SeanP2001/Sunrise_Alarm_Clock_V3/Code/Documentation/latex/App_8h__incl.pdf

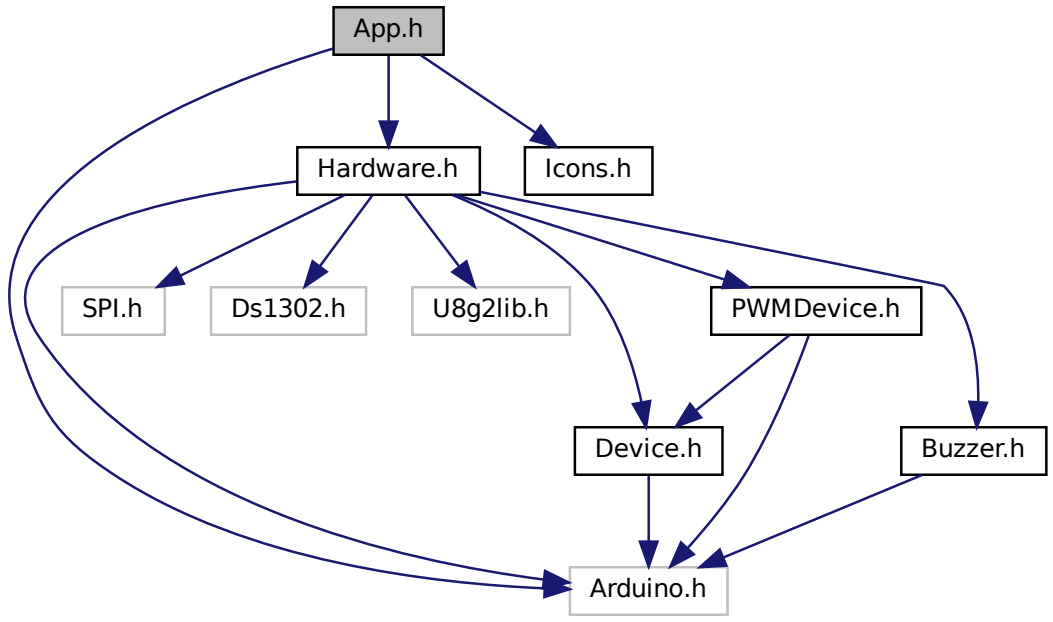
[picture p40: figure]
App.h; Arduino.h; Hardware.h; Icons.h; SPI.h; U8g2lib.h; Device.h; PWMDevice.h; Buzzer.h
