SeanP2001/Sunrise_Alarm_Clock_V3/Code/Documentation/latex/PWMDevice_8cpp__incl.pdf

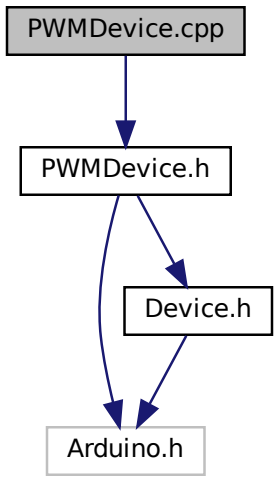
[picture p41: figure]
PWMDevice.cpp; PWMDevice.h; Arduino.h; Device.h
