SeanP2001/Sunrise_Alarm_Clock_V3/Code/Documentation/html/classAlarmApp__coll__graph.png

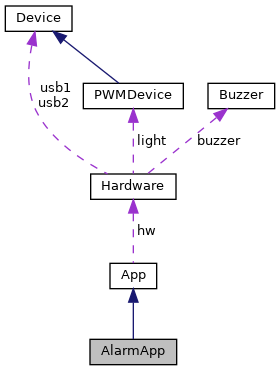
Code/Documentation/html/classAlarmApp__coll__graph.png
