SeanP2001/Sunrise_Alarm_Clock_V3/Code/Documentation/html/classApp__coll__graph.png

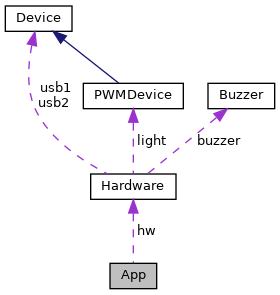
Code/Documentation/html/classApp__coll__graph.png
