SeanP2001/Sunrise_Alarm_Clock_V3/Code/Documentation/html/inherit_graph_0.png

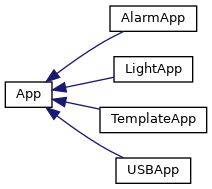
Code/Documentation/html/inherit_graph_0.png
