SeanP2001/Sunrise_Alarm_Clock_V3/Images/Alarm_1.jpg

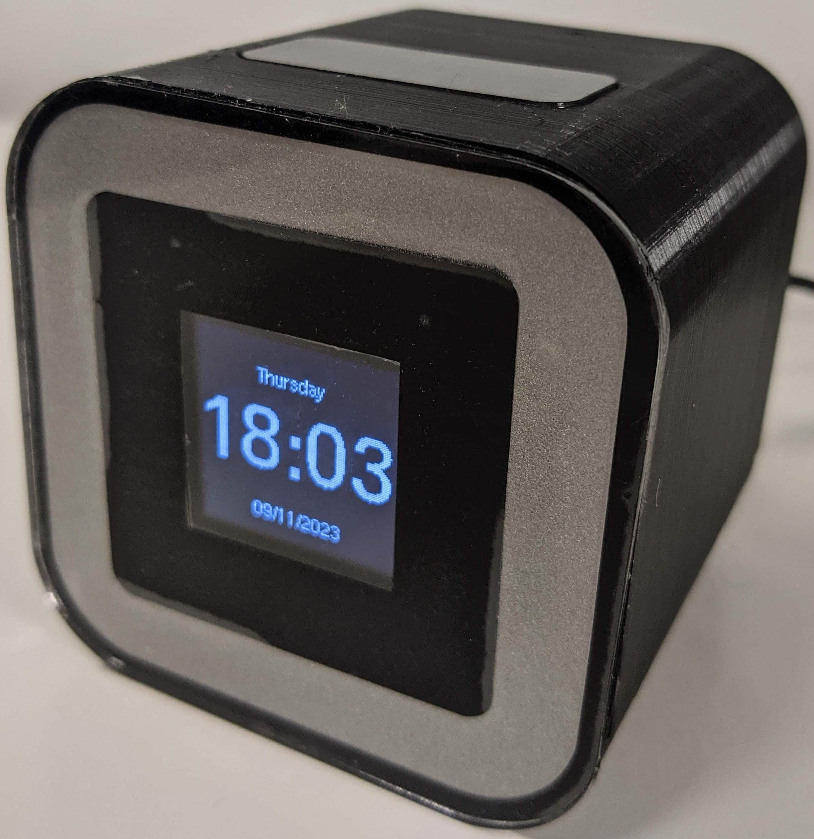
Images/Alarm_1.jpg
