SeanP2001/Sunrise_Alarm_Clock_V3/Images/Alarm_Front_2.jpg

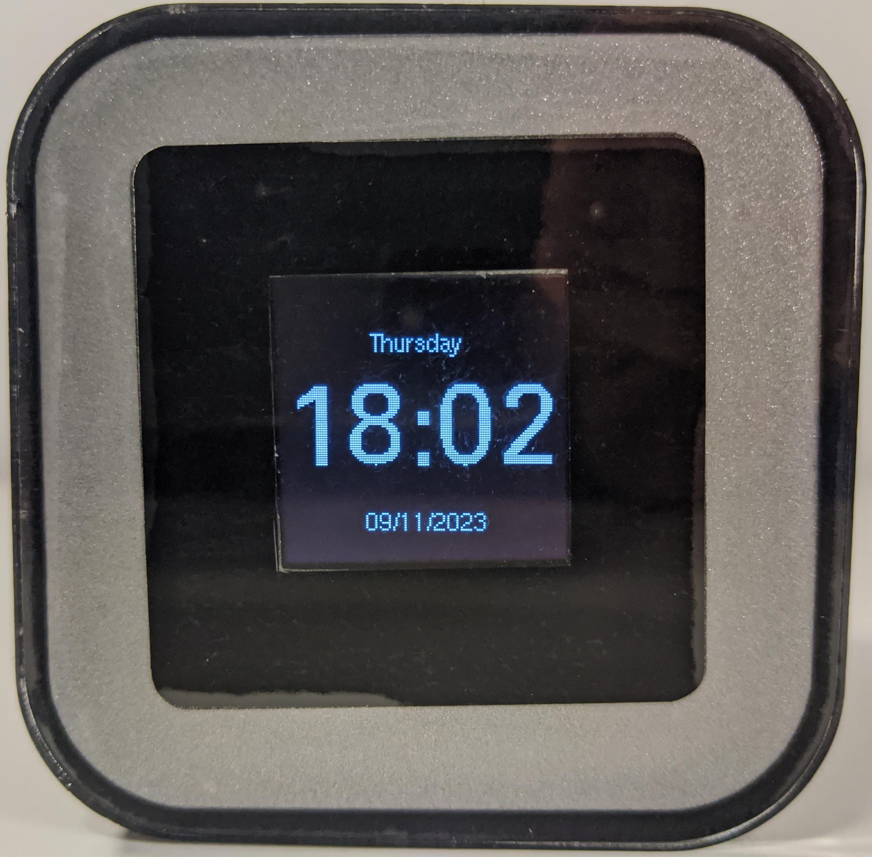
Images/Alarm_Front_2.jpg
