SeanP2001/Sunrise_Alarm_Clock_V3/Images/CAD/Enclosure_Open_Bottom.png

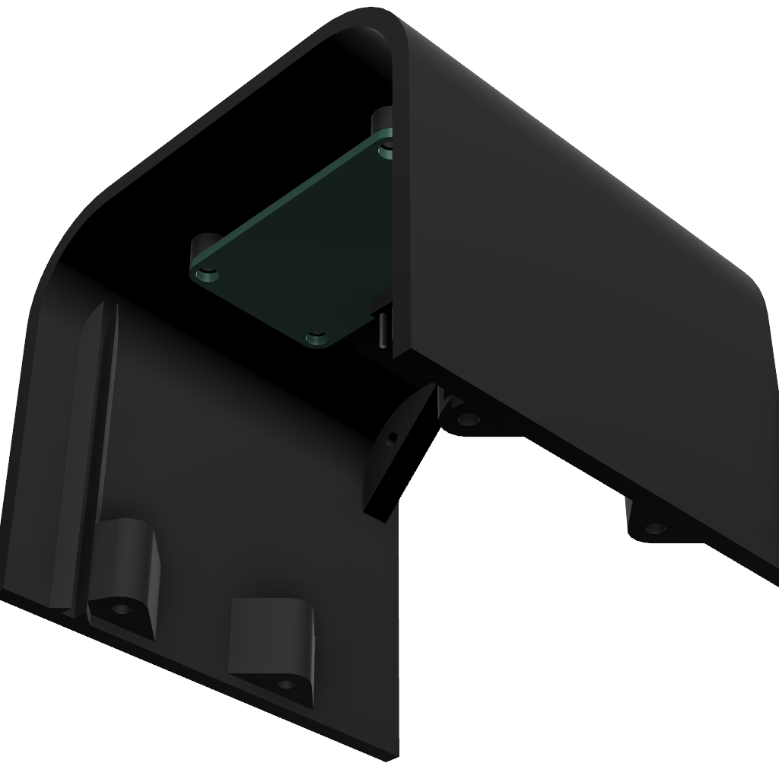
Images/CAD/Enclosure_Open_Bottom.png
