SeanP2001/Sunrise_Alarm_Clock_V3/Images/V2_Alarm_CAD.png

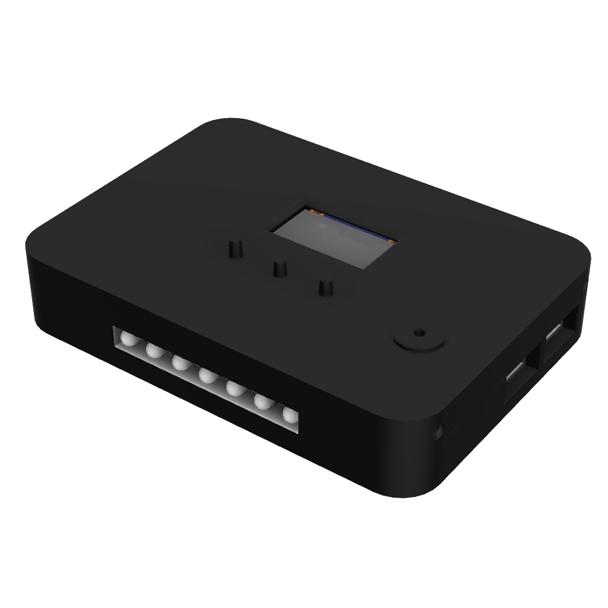
Images/V2_Alarm_CAD.png
