SeanP2001/Sunrise_Alarm_Clock_V3/Code/SunriseAlarm/Icons.h

/**
 * @file Icons.h
 * @author Sean Price
 * @brief Contains icon data for various symbols.
 * @version 0.1
 * @date 13/01/2024
 * 
 * 
 */

// 'alarmOffIcon', 16x16px
const uint8_t alarmOffIcon [] PROGMEM = {
  0x00, 0x80, 0x01, 0xc0, 0x07, 0x70, 0x04, 0x10, 0x0c, 0x18, 0x08, 0x08, 0x08, 0x08, 0x08, 0x08, 
  0x08, 0x08, 0x08, 0x08, 0x18, 0x0c, 0x30, 0x06, 0x60, 0x03, 0x7f, 0xff, 0x00, 0xf0, 0x00, 0x60
};

// 'alarmOnIcon', 16x16px
const uint8_t alarmOnIcon [] PROGMEM = {
  0x00, 0x80, 0x01, 0xc1, 0x47, 0xf2, 0x27, 0xf0, 0x0f, 0xf8, 0x0f, 0xf8, 0x0f, 0xf8, 0x2f, 0xfa, 
  0x4f, 0xf9, 0x8f, 0xf8, 0x1f, 0xfc, 0x3f, 0xfe, 0x7f, 0xff, 0x7f, 0xff, 0x00, 0xf0, 0x00, 0x60
};

// 'lightOffIcon', 96x96px
const uint8_t lightOffIcon [] PROGMEM = {
	0x00, 0x00, 0x00, 0x00, 0x00, 0x00, 0x00, 0x00, 0x00, 0x00, 0x00, 0x00, 0x00, 0x00, 0x00, 0x00, 
	0x00, 0x00, 0x00, 0x00, 0x00, 0x00, 0x00, 0x00, 0x00, 0x00, 0x00, 0x00, 0x00, 0x00, 0x00, 0x00, 
	0x00, 0x00, 0x00, 0x00, 0x00, 0x00, 0x00, 0x00, 0x00, 0x00, 0x00, 0x00, 0x00, 0x00, 0x00, 0x00, 
	0x00, 0x00, 0x00, 0x00, 0x00, 0x00, 0x00, 0x00, 0x00, 0x00, 0x00, 0x00, 0x00, 0x00, 0x00, 0x00, 
	0x00, 0x00, 0x00, 0x00, 0x00, 0x00, 0x00, 0x00, 0x00, 0x00, 0x00, 0x00, 0x00, 0x00, 0x00, 0x00, 
	0x00, 0x00, 0x00, 0x00, 0x00, 0x00, 0x00, 0x00, 0x00, 0x00, 0x00, 0x00, 0x00, 0x00, 0x00, 0x00, 
	0x00, 0x00, 0x00, 0x00, 0x00, 0x00, 0x00, 0x00, 0x00, 0x00, 0x00, 0x00, 0x00, 0x00, 0x00, 0x00, 
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
	0x00, 0x00, 0x00, 0x18, 0x30, 0x00, 0x00, 0x00, 0x00, 0x00, 0x00, 0x18, 0x38, 0x00, 0x00, 0x00, 
	0x00, 0x00, 0x00, 0x38, 0x1c, 0x00, 0x00, 0x00, 0x00, 0x00, 0x00, 0x60, 0x06, 0x00, 0x00, 0x00, 
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
};
