SeanP2001/Sunrise_Alarm_Clock_V3/Code/SunriseAlarm/LightApp.cpp

/**
 * @file LightApp.cpp
 * @author Sean Price
 * @brief Implements the LightApp class.
 * @version 0.1
 * @date 13/01/2024
 * 
 * 
 */

#include "LightApp.h"


//---------------------------------------------------- C O N S T R U C T O R ----------------------------------------------------
LightApp::LightApp(Hardware& hardware) : App(hardware), lightOnTime(6), lightOffTime(9) {} // WARNING: Temporary Magic Numbers (Will be rectified with settings struct)


//----------------------------------------------------------- I N I T -----------------------------------------------------------
void LightApp::init()
{
  return;
}


//---------------------------------------------- D I S P L A Y   M E N U   P A G E -----------------------------------------------
void LightApp::displayMenuPage()
{ 
  hw.display.drawBitmap(16, 16, 12, 96, lightOffIcon);

  // Updates a small part of the display (much faster)
  hw.display.updateDisplayArea(2, 2, 12, 12);  // Works in 8x8 blocks (x, y, w, h)
}


//-------------------------------------------------------- D I S P L A Y --------------------------------------------------------
void LightApp::display() 
{
  hw.display.drawBitmap(16, 16, 12, 96, lightOnIcon);

  // Updates a small part of the display (much faster)
  hw.display.updateDisplayArea(2, 2, 12, 12);  // Works in 8x8 blocks (x, y, w, h) 
}


//---------------------------------------------------- L E F T   A C T I O N ----------------------------------------------------
void LightApp::leftAction() 
{
  hw.light.decreaseLevel();
  hw.light.turnOn();

  return;
}


//-------------------------------------------------- M I D D L E   A C T I O N --------------------------------------------------
void LightApp::middleAction() 
{
  hw.light.turnOff();
  closeApp();
}


//--------------------------------------------------- R I G H T   A C T I O N ---------------------------------------------------
void LightApp::rightAction()
{
  hw.light.increaseLevel();
  hw.light.turnOn();

  return;
}


//------------------------------------------------------- O P E N   A P P -------------------------------------------------------
void LightApp::openApp() 
{
  hw.light.turnOn();
  App::openApp();
}


//----------------------------------------------- B A C K G R O U N D   T A S K S -----------------------------------------------
void LightApp::backgroundTasks()
{
  hw.rtc.getDateTime(&now);                // Update the time

  
  // If the Light is due to be on (This will all be streamlined when the datetime class is added (comparisons))
  if(lightOnTime < lightOffTime)
  {
    if((now.hour >= lightOnTime) && (now.hour < lightOffTime))  // if the current hour is between the on and off hour
    {
      hw.light.turnOnFull();
    }
  }
  if(lightOnTime > lightOffTime)
  {
    if((now.hour >= lightOnTime && now.hour <= 23) || (now.hour >= 0 && now.hour < lightOffTime))     // if it is after the on time at night or before the off time in the morning
    {
      hw.light.turnOnFull();
    }
  }
  
  if((now.hour == lightOffTime) && now.minute == 0)
  {
    hw.light.turnOff();
  }

  return;
}
